Alan-Lomax/RFID_Tag_Scanner/data/05 Picture of test rig (without the box).jpg

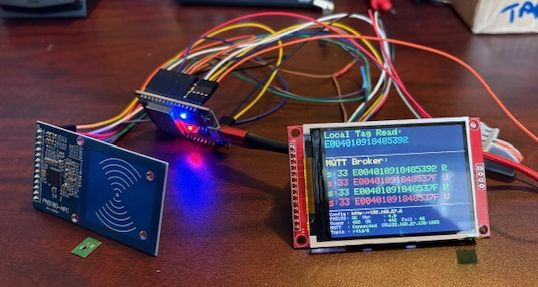
data/05 Picture of test rig (without the box).jpg
