Alan-Lomax/RFID_Tag_Scanner/data/Details/ESP Wroom32 Dev board Tech Spec.jpg

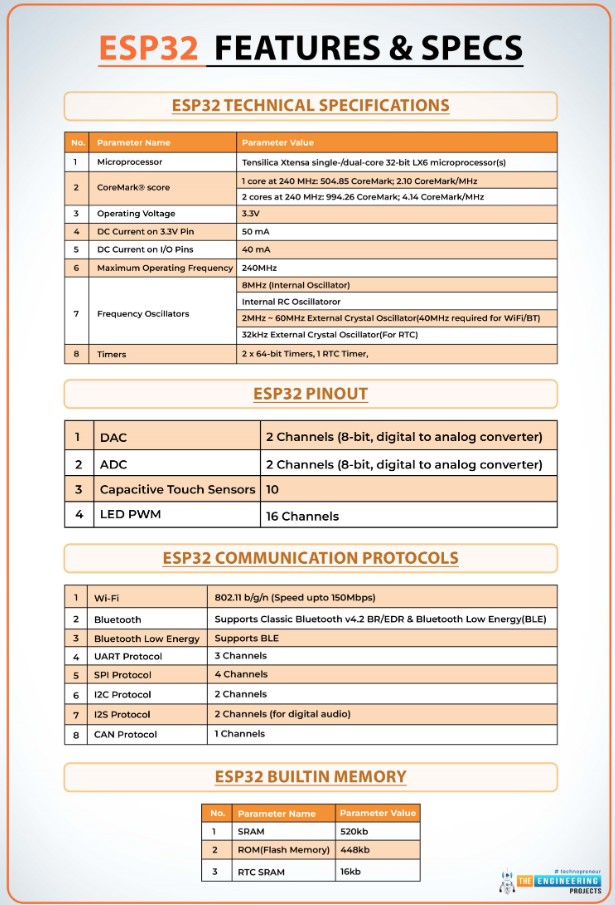
data/Details/ESP Wroom32 Dev board Tech Spec.jpg
