Alan-Lomax/RFID_Tag_Scanner/data/01 RFID Scanner Schematic Jan 2026.jpg

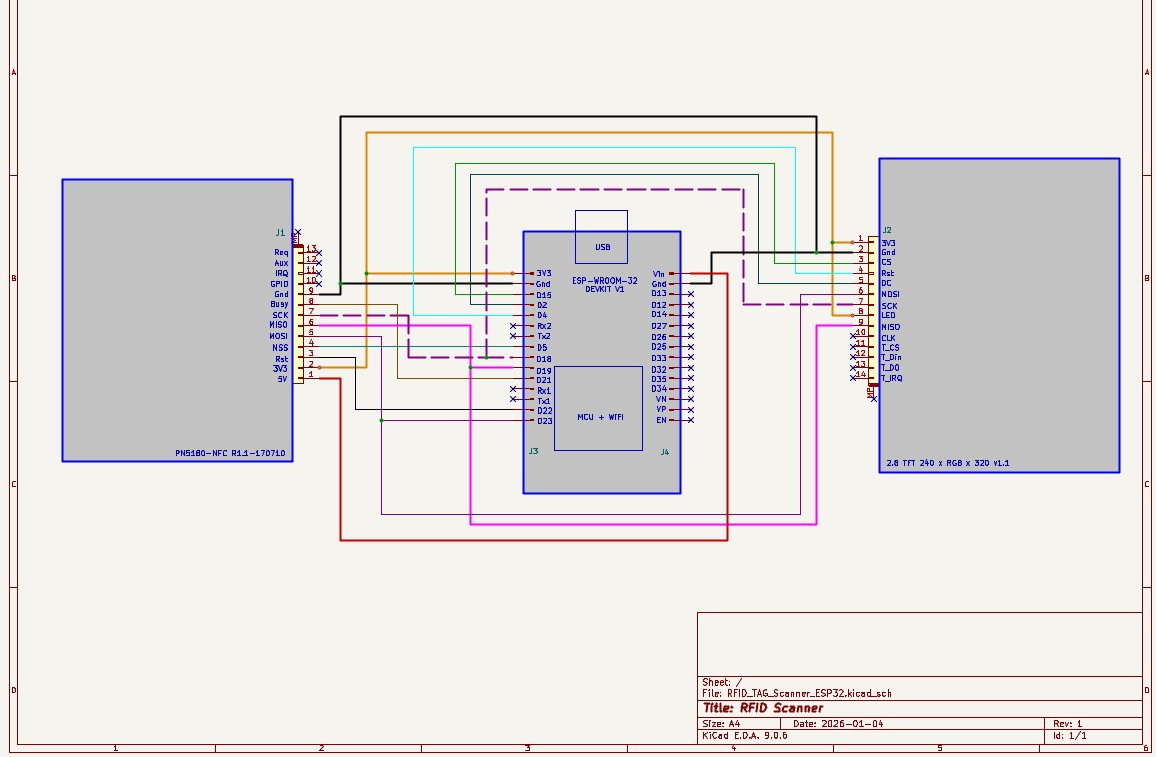
data/01 RFID Scanner Schematic Jan 2026.jpg
