Alan-Lomax/RFID_Tag_Scanner/data/10 Three Quarter Front View.JPG

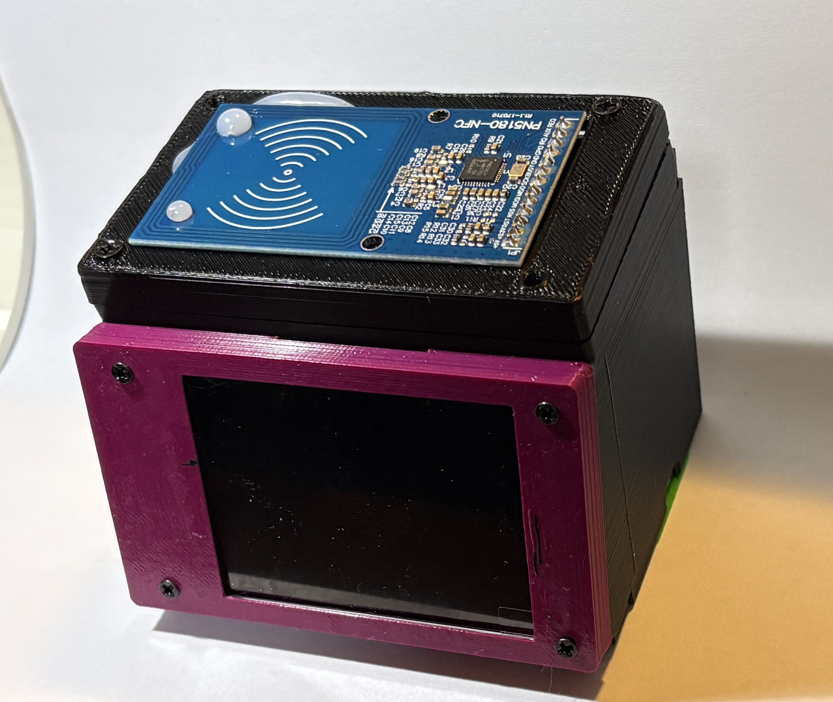
data/10 Three Quarter Front View.JPG
