Alan-Lomax/RFID_Tag_Scanner/data/11 Front View of Box.JPG

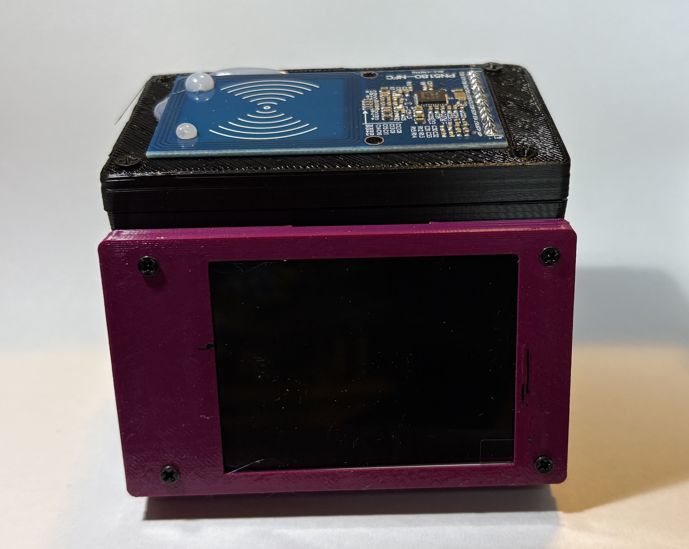
data/11 Front View of Box.JPG
