Alan-Lomax/RFID_Tag_Scanner/data/12 End View of Box with USB port.JPG

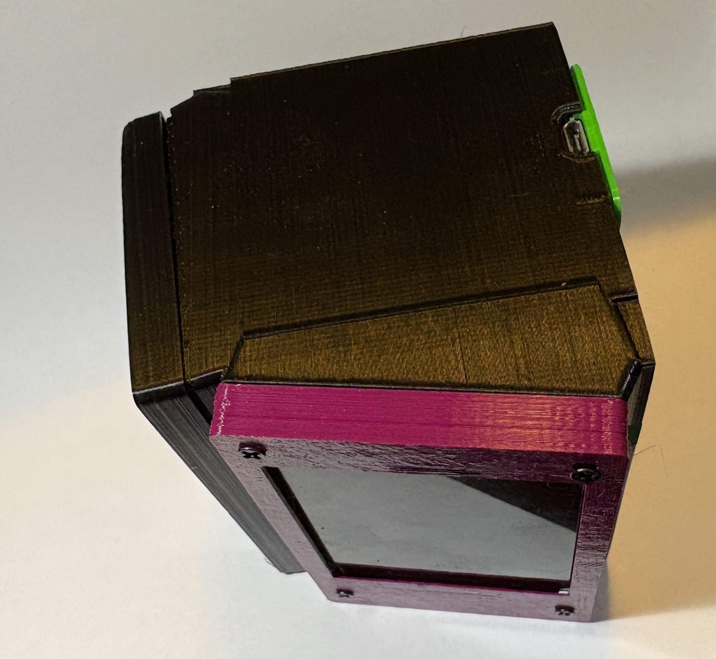
data/12 End View of Box with USB port.JPG
