Alan-Lomax/RFID_Tag_Scanner/data/13 Bottom View Showing ESP Cover.JPG

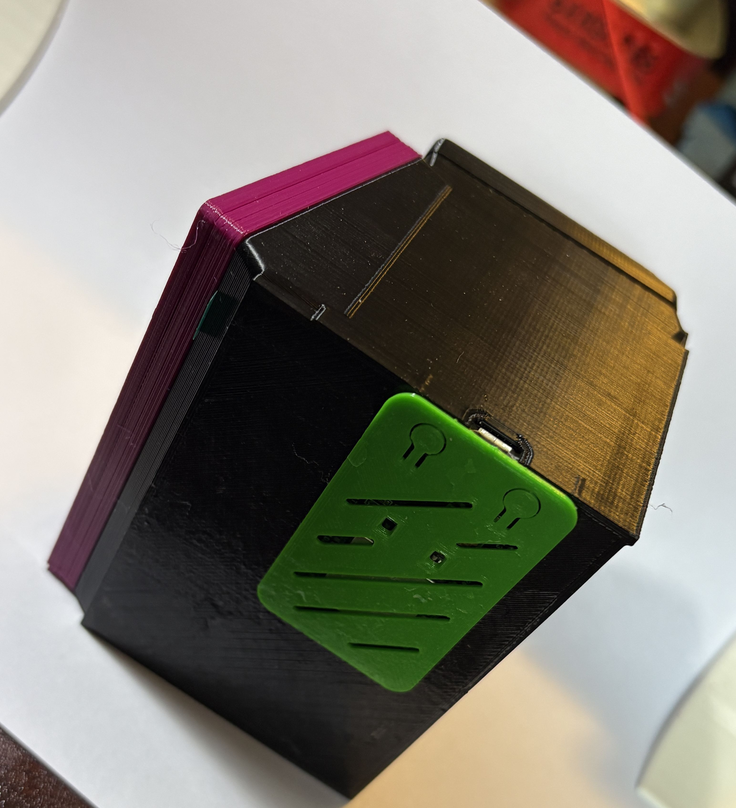
data/13 Bottom View Showing ESP Cover.JPG
