Alan-Lomax/RFID_Tag_Scanner/data/14 Bottom Front View.JPG

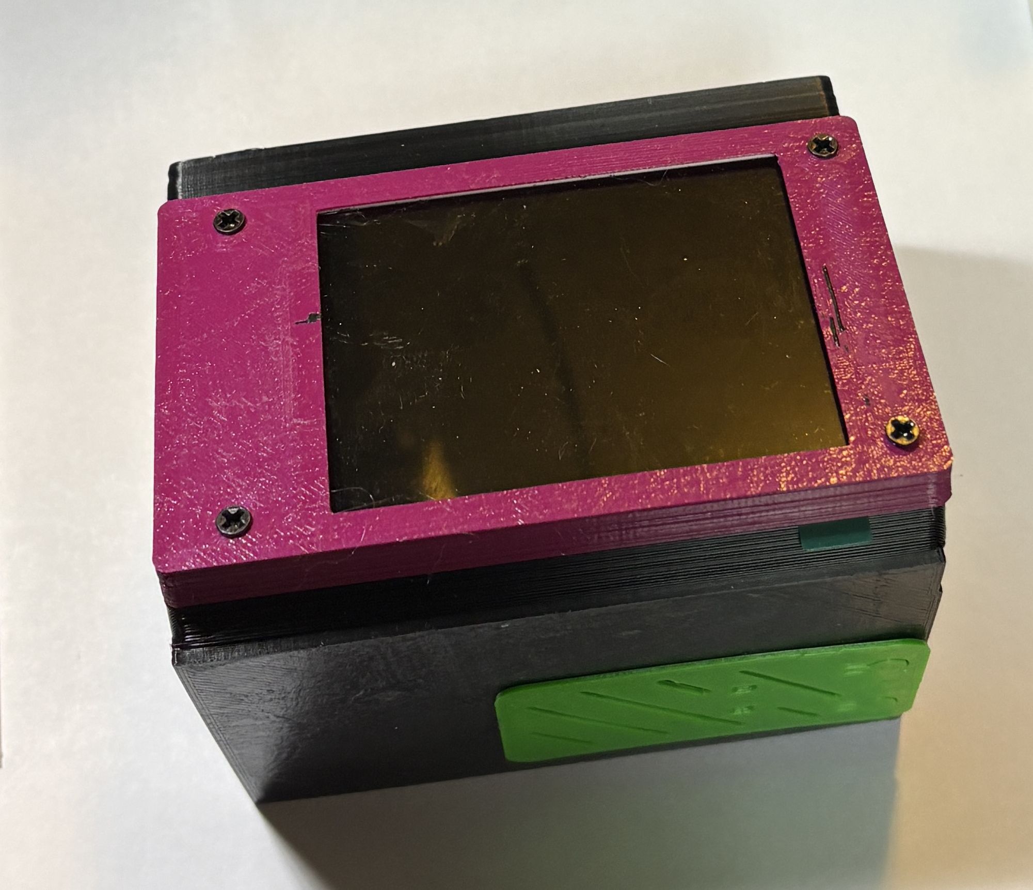
data/14 Bottom Front View.JPG
