Alan-Lomax/RFID_Tag_Scanner/data/15 Top View with Hot Glue.JPG

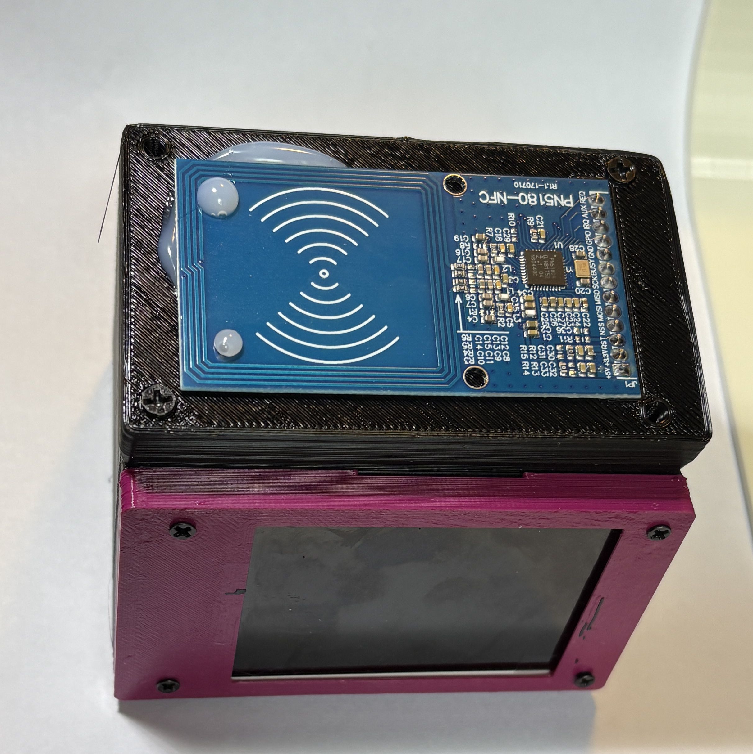
data/15 Top View with Hot Glue.JPG
