Alan-Lomax/RFID_Tag_Scanner/data/Details/2.8 inch TFT Display 240x320 ST7789V.jpg

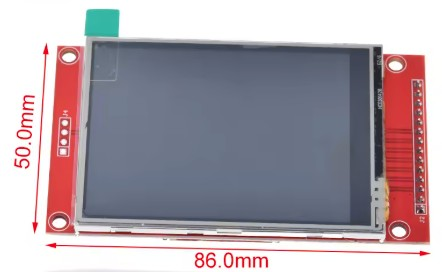
data/Details/2.8 inch TFT Display 240x320 ST7789V.jpg
