Alan-Lomax/RFID_Tag_Scanner/data/Details/ESP Wroom32 Dev board Pin Out.jpg

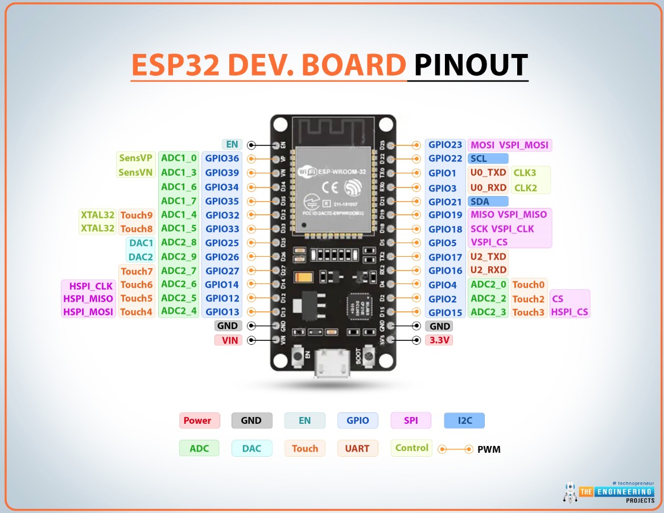
data/Details/ESP Wroom32 Dev board Pin Out.jpg
