Alan-Lomax/RFID_Tag_Scanner/data/Details/PN5180-NFC.jpg

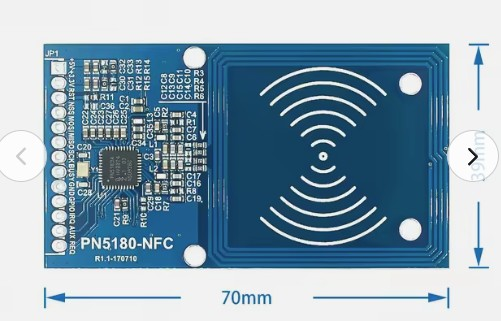
data/Details/PN5180-NFC.jpg
